Propato/trabalhos-Ufes-PIC-II/Estrutura/Auriculaire3.stl

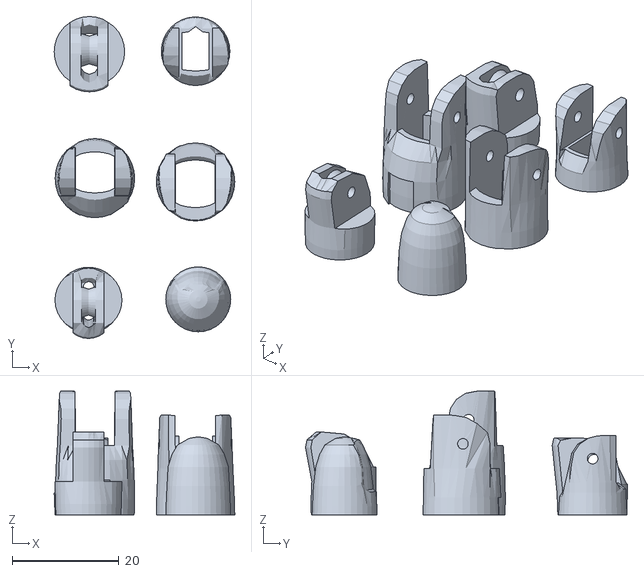
[picture p22: CAD file, 2025-08-25]
Estrutura/Auriculaire3.stl
33.8 x 60.3 x 23.2
