Propato/trabalhos-Ufes-PIC-II/Estrutura/WristsmallV4.stl

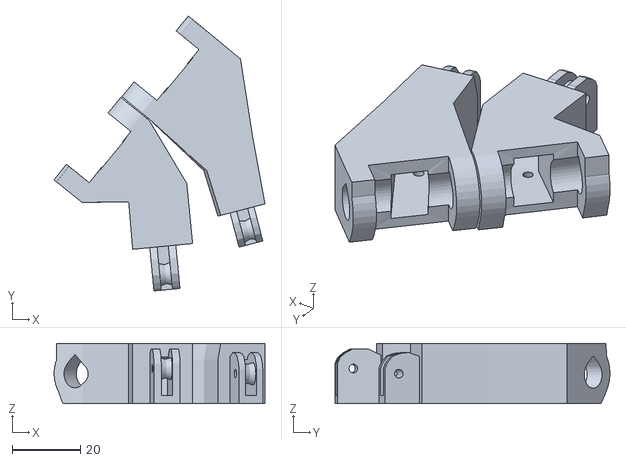
[picture p23: CAD file, 2025-08-25]
Estrutura/WristsmallV4.stl
62.0 x 80.8 x 17.7
