Propato/trabalhos-Ufes-PIC-II/Estrutura/Bolt_entretoise7.stl

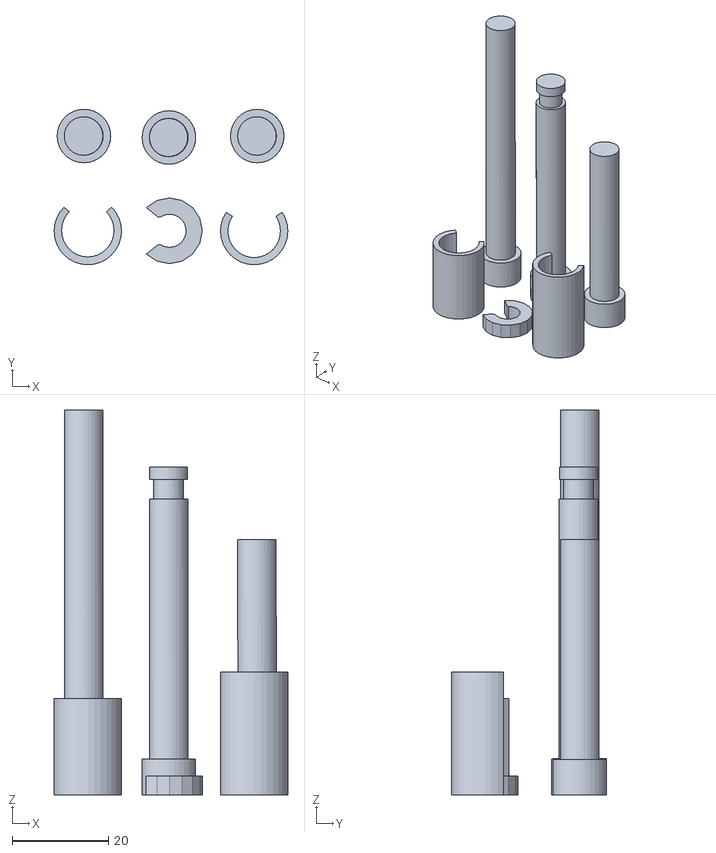
[picture p24: CAD file, 2025-08-25]
Estrutura/Bolt_entretoise7.stl
48.5 x 32.3 x 79.9
